Wierzbowsky/GotekLEDScreenClock/Pics/20231015_130555.jpg

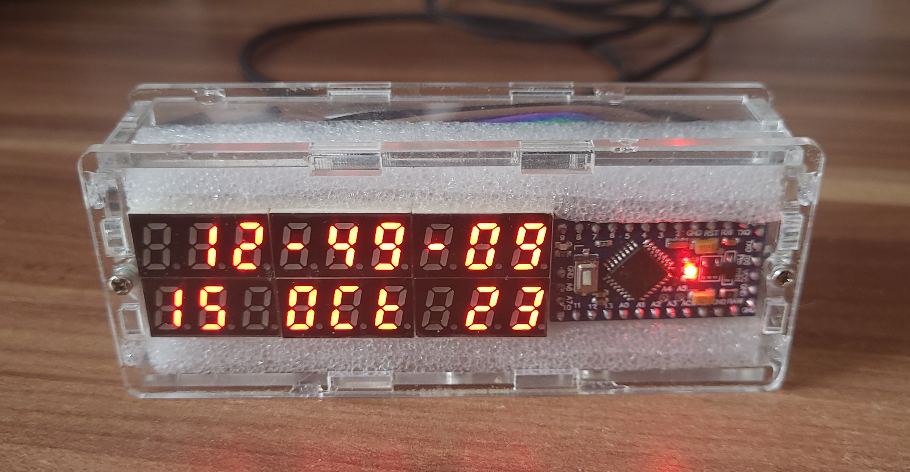
Pics/20231015_130555.jpg
